garberw/weather_station_home_made/Arduino/utility_bme688/utility_bme688.ino

#include "Adafruit_EEPROM_I2C.h"
// #include "Adafruit_FRAM_I2C.h"
// #include <EEPROM.h>
#include "bsec.h"
/* Configure the BSEC library with information about the sensor
    18v/33v = Voltage at Vdd. 1.8V or 3.3V
    3s/300s = BSEC operating mode, BSEC_SAMPLE_RATE_LP or BSEC_SAMPLE_RATE_ULP
    4d/28d = Operating age of the sensor in days
    generic_18v_3s_4d
    generic_18v_3s_28d
    generic_18v_300s_4d
    generic_18v_300s_28d
    generic_33v_3s_4d
    generic_33v_3s_28d
    generic_33v_300s_4d
    generic_33v_300s_28d
*/
const uint8_t bsec_config_iaq[] = {
#include "config/generic_33v_3s_4d/bsec_iaq.txt"
};


// #define STATE_SAVE_PERIOD	UINT32_C(360 * 60 * 1000) // 360 minutes - 4 times a day
#define STATE_SAVE_PERIOD	UINT32_C(10 * 60 * 1000) // 10 minutes - 144 times a day

// Helper functions declarations
void checkIaqSensorStatus(void);
void loadState(void);
void updateState(void);

// Create an object of the class Bsec
Bsec iaqSensor;
uint8_t bsecState[BSEC_MAX_STATE_BLOB_SIZE] = {0};
uint16_t stateUpdateCounter = 0;
Adafruit_EEPROM_I2C EEPROM;

String output;

// Entry point for the example
void setup(void)
{
  Serial.begin(115200);
  while (!Serial);
  // EEPROM.begin(BSEC_MAX_STATE_BLOB_SIZE + 1);
	if (EEPROM.begin(0x50)) {
    Serial.println("found EEPROM");
    Serial.flush();
	} else {
    Serial.println("no EEPROM.  halt.");
    Serial.flush();
    while (1) delay(1000);
	}
  delay(1000);
  iaqSensor.begin(BME68X_I2C_ADDR_HIGH, Wire);
  output = "\nBSEC library version " + String(iaqSensor.version.major) + "." + String(iaqSensor.version.minor) + "." + String(iaqSensor.version.major_bugfix) + "." + String(iaqSensor.version.minor_bugfix);
  Serial.println(output);
  checkIaqSensorStatus();

  iaqSensor.setConfig(bsec_config_iaq);
  checkIaqSensorStatus();

  loadState();

  bsec_virtual_sensor_t sensorList[13] = {
    BSEC_OUTPUT_IAQ,
    BSEC_OUTPUT_STATIC_IAQ,
    BSEC_OUTPUT_CO2_EQUIVALENT,
    BSEC_OUTPUT_BREATH_VOC_EQUIVALENT,
    BSEC_OUTPUT_RAW_TEMPERATURE,
    BSEC_OUTPUT_RAW_PRESSURE,
    BSEC_OUTPUT_RAW_HUMIDITY,
    BSEC_OUTPUT_RAW_GAS,
    BSEC_OUTPUT_STABILIZATION_STATUS,
    BSEC_OUTPUT_RUN_IN_STATUS,
    BSEC_OUTPUT_SENSOR_HEAT_COMPENSATED_TEMPERATURE,
    BSEC_OUTPUT_SENSOR_HEAT_COMPENSATED_HUMIDITY,
    BSEC_OUTPUT_GAS_PERCENTAGE
  };

  iaqSensor.updateSubscription(sensorList, 13, BSEC_SAMPLE_RATE_LP);
  checkIaqSensorStatus();

  // Print the header
  output = "Timestamp [ms], IAQ, IAQ accuracy, Static IAQ, CO2 equivalent, breath VOC equivalent, raw temp[°C], pressure [hPa], raw relative humidity [%], gas [Ohm], Stab Status, run in status, comp temp[°C], comp humidity [%], gas percentage";
  Serial.println(output);
}

// Function that is looped forever
void loop(void)
{
  unsigned long time_trigger = millis();
  if (iaqSensor.run()) { // If new data is available
    output = String(time_trigger);
    output += ", " + String(iaqSensor.iaq);
    output += ", " + String(iaqSensor.iaqAccuracy);
    output += ", " + String(iaqSensor.staticIaq);
    output += ", " + String(iaqSensor.co2Equivalent);
    output += ", " + String(iaqSensor.breathVocEquivalent);
    output += ", " + String(iaqSensor.rawTemperature);
    output += ", " + String(iaqSensor.pressure);
    output += ", " + String(iaqSensor.rawHumidity);
    output += ", " + String(iaqSensor.gasResistance);
    output += ", " + String(iaqSensor.stabStatus);
    output += ", " + String(iaqSensor.runInStatus);
    output += ", " + String(iaqSensor.temperature);
    output += ", " + String(iaqSensor.humidity);
    output += ", " + String(iaqSensor.gasPercentage);
    Serial.println(output);
    updateState();
  } else {
    checkIaqSensorStatus();
  }
}

// Helper function definitions
void checkIaqSensorStatus(void)
{
  if (iaqSensor.bsecStatus != BSEC_OK) {
    if (iaqSensor.bsecStatus < BSEC_OK) {
      output = "BSEC error code : " + String(iaqSensor.bsecStatus);
      Serial.println(output);
      for (;;) {
        delay(1000);
      }
    } else {
      output = "BSEC warning code : " + String(iaqSensor.bsecStatus);
      Serial.println(output);
    }
  }

  if (iaqSensor.bme68xStatus != BME68X_OK) {
    if (iaqSensor.bme68xStatus < BME68X_OK) {
      output = "BME68X error code : " + String(iaqSensor.bme68xStatus);
      Serial.println(output);
      for (;;) {
        delay(1000);
      }
    } else {
      output = "BME68X warning code : " + String(iaqSensor.bme68xStatus);
      Serial.println(output);
    }
  }
}

void loadState(void)
{
  if (EEPROM.read(0) == BSEC_MAX_STATE_BLOB_SIZE) {
    // Existing state in EEPROM
    Serial.println("Reading state from EEPROM");

    for (uint8_t i = 0; i < BSEC_MAX_STATE_BLOB_SIZE; i++) {
      bsecState[i] = EEPROM.read(i + 1);
      Serial.println(bsecState[i], HEX);
    }

    iaqSensor.setState(bsecState);
    checkIaqSensorStatus();
  } else {
    // Erase the EEPROM with zeroes
    Serial.println("Erasing EEPROM");

    for (uint8_t i = 0; i < BSEC_MAX_STATE_BLOB_SIZE + 1; i++)
      EEPROM.write(i, 0);

    // EEPROM.commit();
  }
}

void updateState(void)
{
  bool update = false;
  if (stateUpdateCounter == 0) {
    /* First state update when IAQ accuracy is >= 3 */
    if (iaqSensor.iaqAccuracy >= 3) {
      update = true;
      stateUpdateCounter++;
    }
  } else {
    /* Update every STATE_SAVE_PERIOD minutes */
    if ((stateUpdateCounter * STATE_SAVE_PERIOD) < millis()) {
      update = true;
      stateUpdateCounter++;
    }
  }

  if (update) {
    iaqSensor.getState(bsecState);
    checkIaqSensorStatus();

    Serial.println("Writing state to EEPROM");

    for (uint8_t i = 0; i < BSEC_MAX_STATE_BLOB_SIZE ; i++) {
      EEPROM.write(i + 1, bsecState[i]);
      Serial.println(bsecState[i], HEX);
    }

    EEPROM.write(0, BSEC_MAX_STATE_BLOB_SIZE);
    // EEPROM.commit();
  }
}
